Bread80/CPCModular/Sound/CPCSound - Copy.kicad_pcb

## KiCad design Sound/CPCSound - Copy.kicad_pcb (2023-09-27, an earlier design)

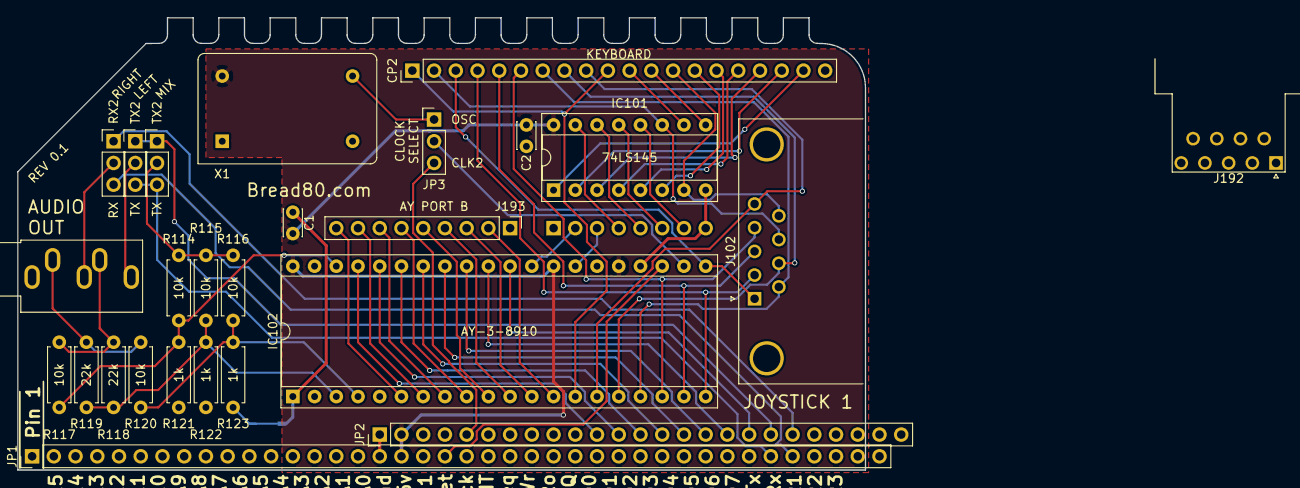
[picture p34: board CPCSound - Copy.kicad_pcb from above]

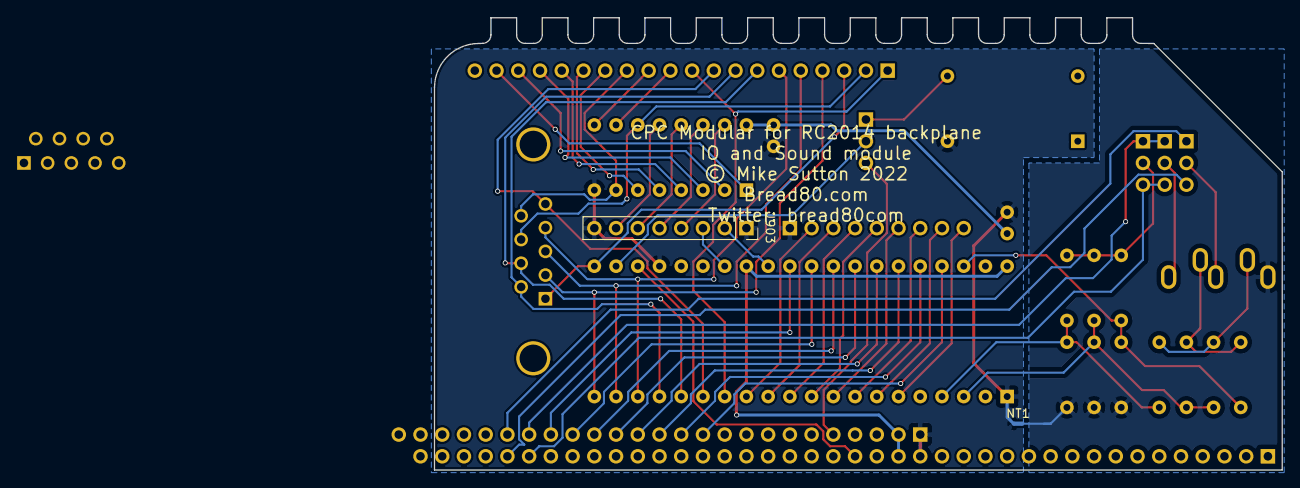
[picture p35: board CPCSound - Copy.kicad_pcb from below]

Board: 2 copper layers, 99.1 x 52.9 mm, 28 parts (2 on the bottom side), 59 nets.

Parts:
C1, C2: 0.1nF; C_Disc_D3.0mm_W2.0mm_P2.50mm
CP2: Keyboard Connector (20-way inline 2.54mm); PinHeader_1x20_P2.54mm_Vertical
IC101: 74LS145; DIP-16_W7.62mm_Socket
IC102: AY-3-8910; DIP-40_W15.24mm_Socket
J102: Paddle Port (9-Pin D); DSUB-9_Male_Horizontal_P2.77x2.84mm_EdgePinOffset9.90mm_Hou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
J103: AudioJack3_Ground_SwitchTR; Jack_3.5mm_CUI_SJ1-3535NG_Horizontal
J192: Paddle Port 2 (9-Pin D); DSUB-9_Male_Horizontal_P2.77x2.84mm_EdgePinOffset9.40mm
J193: Conn_01x09_Male; PinHeader_1x09_P2.54mm_Vertical
J903: Conn_01x08_Female; PinSocket_1x08_P2.54mm_Vertical
JP1: RC2014Bus; PinHeader_1x40_P2.54mm_Vertical
JP2: RC2014ExtendedBus; PinHeader_1x25_P2.54mm_Vertical
JP3: Osc sel; PinHeader_1x03_P2.54mm_Vertical
JP4: MIX; PinHeader_1x03_P2.54mm_Vertical
JP5: LEFT; PinHeader_1x03_P2.54mm_Vertical
JP6: RIGHT; PinHeader_1x03_P2.54mm_Vertical
NT1: Net-Tie_2; NetTie-2_SMD_Pad0.5mm
R114, R115, R116, R117, R120: 10k; R_Axial_DIN0207_L6.3mm_D2.5mm_P7.62mm_Horizontal
R118, R119: 22k; R_Axial_DIN0207_L6.3mm_D2.5mm_P7.62mm_Horizontal
R121, R122, R123: 1k; R_Axial_DIN0207_L6.3mm_D2.5mm_P7.62mm_Horizontal
X1: CXO_DIP14_1MHz; Oscillator_DIP-14

Connections:
+5V: C1.1, C2.1, IC101.16, IC102.25, IC102.28, IC102.40, JP1.18, JP2.2, X1.14
/IO_SOUND/A: IC102.4, R116.1, R120.2, R123.2
/IO_SOUND/ALEFT: J103.TN, JP5.2
/IO_SOUND/ARIGHT: J103.RN, JP6.2
/IO_SOUND/AYA0: CP2.3, IC102.21, J102.1, J192.1
/IO_SOUND/AYA1: CP2.4, IC102.20, J102.2, J192.2
/IO_SOUND/AYA2: CP2.5, IC102.19, J102.3, J192.3
/IO_SOUND/AYA3: CP2.6, IC102.18, J102.4, J192.4
/IO_SOUND/AYA4: CP2.7, IC102.17, J102.6, J192.5
/IO_SOUND/AYA5: CP2.8, IC102.16, J102.7, J192.6
/IO_SOUND/AYA6: CP2.9, IC102.15, J102.5, J192.7
/IO_SOUND/AYA7: CP2.1, CP2.10, IC102.14
/IO_SOUND/B: IC102.3, R115.1, R118.2, R119.2, R122.2
/IO_SOUND/BC1: IC102.29, J903.2
/IO_SOUND/BDIR: IC102.27, J903.3
/IO_SOUND/C: IC102.38, R114.1, R117.2, R121.2
/IO_SOUND/COMMON: CP2.2, IC101.11, J102.8, J192.9
/IO_SOUND/COM_2: CP2.13, IC101.7, J102.9, J192.8
/IO_SOUND/SOUND: JP4.2, R114.2, R115.2, R116.2
/IO_SOUND/SOUND_CLK: JP2.5, JP3.3
/IO_SOUND/Y1: CP2.19, IC101.1
/IO_SOUND/Y2: CP2.18, IC101.2
/IO_SOUND/Y3: CP2.17, IC101.3
/IO_SOUND/Y4: CP2.16, IC101.4
/IO_SOUND/Y5: CP2.15, IC101.5
/IO_SOUND/Y6: CP2.14, IC101.6
/IO_SOUND/Y8: CP2.12, IC101.9
/IO_SOUND/Y9: CP2.11, IC101.10
/IO_SOUND/~RESET: IC102.23, JP1.20
GND: C1.2, C2.2, IC101.8, IC102.1, IC102.24, J193.1, J903.1, J903.8, JP1.17, JP2.1, NT1.1, X1.7
GNDA: J103.S, NT1.2, R121.1, R122.1, R123.1
unnamed: IC102.6, J193.9
unnamed: IC102.7, J193.8
unnamed: IC102.8, J193.7
unnamed: IC102.9, J193.6
unnamed: IC102.10, J193.5
unnamed: IC102.11, J193.4
unnamed: IC102.12, J193.3
unnamed: IC102.13, J193.2
unnamed: IC102.22, JP3.2
unnamed: J103.R, R117.1, R118.1
unnamed: J103.T, R119.1, R120.1
unnamed: JP1.35, JP4.3, JP5.3
unnamed: JP1.36, JP6.3
unnamed: JP2.19, JP4.1, JP5.1
unnamed: JP2.20, JP6.1
unnamed: JP3.1, X1.8
PA0: IC102.37, JP2.11
PA1: IC102.36, JP2.12
PA2: IC102.35, JP2.13
PA3: IC102.34, JP2.14
PA4: IC102.33, JP2.15
PA5: IC102.32, JP2.16
PA6: IC102.31, JP2.17
PA7: IC102.30, JP2.18
PC0: IC101.15, J903.4
PC1: IC101.14, J903.5
PC2: IC101.13, J903.6
PC3: IC101.12, J903.7
